begrie/Radiator_Froeling_P2_S3100_ESP32/src/serial.cpp

#include "serial.h"

#include <stdio.h>
#include <unistd.h>
#include <iostream>
#include <fcntl.h>
#include <termios.h>
#include <sys/ioctl.h>
#include <sys/select.h>

namespace radiator
{
    // #define SERIAL_TO_RADIATOR_RX 16_PIN // ESP32-standard: 16
    // #define SERIAL_TO_RADIATOR_TX 17_PIN // ESP32-standard: 17

    /*
     * Constructor.
     *
     * Opens and initializes the serial port.
     *
     * @param devicename The filename of the serial port device.
     * @return void
     */
    SerialPort::SerialPort(std::string_view devicename)
    {
        if (devicename == "Serial")
            Serial_to_Radiator = &Serial;
        else if (devicename == "Serial1")
            Serial_to_Radiator = &Serial1;
        else if (devicename == "Serial2")
            Serial_to_Radiator = &Serial2;
        else
        {
            ::perror("open_port: Unable to open serial port");
            throw("Unable to open serial port");
        }

        Serial_to_Radiator->begin(SERIAL_TO_RADIATOR_BAUD, SERIAL_8N1, SERIAL_TO_RADIATOR_RX_PIN, SERIAL_TO_RADIATOR_TX_PIN);

        std::cerr << millis() << " ms: Opened serial port " << devicename << " with " << SERIAL_TO_RADIATOR_BAUD << " baud and SERIAL_8N1 for connection to radiator Froeling P2/S3100 -> wait for answer ..." << std::endl;
    }

    /**
     * Destructor.
     */
    SerialPort::~SerialPort()
    {
        if (this->Serial_to_Radiator)
        {
            Serial_to_Radiator->end();
        }
    }

    /**
     * Writes the given data to the serial device.
     *
     * @param data The data to send.
     * @param len The number of bytes to send.
     * @return len on success or -1 on error.
     */
    int SerialPort::write(const uint8_t *data, size_t len)
    {
        if (Serial_to_Radiator)
        {
            const uint8_t *pos = data;
            size_t left = len;

            while (left > 0)
            {
                int written = Serial_to_Radiator->write(pos, left);
                // if (written < 0)
                if (written <= 0)
                {
                    return -1;
                }

                left -= written;
                pos += written;
            }
        }

        return len;
    }

    /**
     * Reads data from the serial port if available.
     *
     * @param buffer The buffer to write data to.
     * @param maxlen The maximum number of bytes to read.
     * @return The number of bytes read or -1 on error.
     */
    int SerialPort::read(uint8_t *data, size_t maxlen)
    {
        int bytes;

        bytes = Serial_to_Radiator->available();
        if (bytes > 0)
        {
            // bytes = Serial_to_Radiator->read(data, maxlen); // read is non-blocking
            bytes = Serial_to_Radiator->readBytes(data, maxlen); // readBytes is blocking and wait for maxlen or timeout from Serial
        }

        return bytes;
    }

    /**
     * Wait for input being available.
     *
     * @param timeout_msec The maximum number of milliseconds to wait.
     * @return -1 on error, 0 if timeout occured. 1 if data available.
     */
    int SerialPort::waitForInput(int timeout_msec)
    {
        if (!Serial_to_Radiator)
            return -1;

        auto _start = millis();
        auto _timeout_ms = (uint32_t)timeout_msec;

        while ((uint32_t)(millis() - _start) < _timeout_ms) // safe wrap-around arithmetic for uint32_t
        {
            if (Serial_to_Radiator->available())
            {
                return 1;
            }
            vTaskDelay(pdMS_TO_TICKS(5));
        }

        return 0;
    }

}
