begrie/Radiator_Froeling_P2_S3100_ESP32/src/serial.h

#ifndef __DH_SERIAL_H__
#define __DH_SERIAL_H__

#include "config.h"

#include <HardwareSerial.h> //ESP-lib

#include <inttypes.h>
#include <stdlib.h>
#include <string>

namespace radiator
{

    class SerialPort
    {
    public:
        SerialPort(std::string_view devicename);
        virtual ~SerialPort();

        int write(const uint8_t *data, size_t len);
        int read(uint8_t *data, size_t maxlen);

        int waitForInput(int timeout_msec);

    protected:
        HardwareSerial *Serial_to_Radiator = NULL;
    };

}

#endif
